harry48225/octoplant/firmware/src/MoistureManager.h

#ifndef MOISTURE_MANAGER
#define MOISTURE_MANAGER

namespace MoistureManager {
  extern void setup();
  extern int getNormalisedReading(); // Returns moisture between 0-12 inclusive
  extern int getRawReading(); // Returns raw moisture reading
}

#endif
